93Urbano/WBC/SW/Wifi_web/Wifi_web.ino

/*
 WiFi Web Server LED Blink

 A simple web server that lets you blink an LED via the web.
 This sketch will print the IP address of your WiFi Shield (once connected)
 to the Serial monitor. From there, you can open that address in a web browser
 to turn on and off the LED on pin 5.

 If the IP address of your shield is yourAddress:
 http://yourAddress/H turns the LED on
 http://yourAddress/L turns it off

 This example is written for a network using WPA2 encryption. For insecure
 WEP or WPA, change the Wifi.begin() call and use Wifi.setMinSecurity() accordingly.

 Circuit:
 * WiFi shield attached
 * LED attached to pin 5

 created for arduino 25 Nov 2012
 by Tom Igoe

ported for sparkfun esp32 
31.01.2017 by Jan Hendrik Berlin
 
 */

#include <WiFi.h>

//concatenacion de cadenas
#include <iostream>
#include <cstdio>  

const char* ssid     = "Galaxy S20+b24a";
const char* password = "davidjimenez";

WiFiServer server(80);

// Variable to store the HTTP request
String header;

// Auxiliar variables to store the current output state
String output26State = "off";
String output27State = "off";

// Assign output variables to GPIO pins
const int output26 = 0;
const int output27 = 1;

void setup()
{
    Serial.begin(115200);

    delay(10);

    // We start by connecting to a WiFi network

    Serial.println();
    Serial.println();
    Serial.print("Connecting to ");
    Serial.println(ssid);

    WiFi.begin(ssid, password);

    while (WiFi.status() != WL_CONNECTED) {
        delay(500);
        Serial.print(".");
    }

    // Initialize the output variables as outputs
    pinMode(output26, OUTPUT);
    pinMode(output27, OUTPUT);
    // Set outputs to LOW
    digitalWrite(output26, LOW);
    digitalWrite(output27, LOW);

    Serial.println("");
    Serial.println("WiFi connected.");
    Serial.println("IP address: ");
    Serial.println(WiFi.localIP());
    
    server.begin();

}

void loop(){
 WiFiClient client = server.available();   // listen for incoming clients

  if (client) {                             // if you get a client,
    Serial.println("New Client.");           // print a message out the serial port
    String currentLine = "";                // make a String to hold incoming data from the client
    while (client.connected()) {            // loop while the client's connected
      if (client.available()) {             // if there's bytes to read from the client,
        char c = client.read();             // read a byte, then
        Serial.write(c);                    // print it out the serial monitor
        if (c == '\n') {                    // if the byte is a newline character

          // if the current line is blank, you got two newline characters in a row.
          // that's the end of the client HTTP request, so send a response:
          if (currentLine.length() == 0) {
            // HTTP headers always start with a response code (e.g. HTTP/1.1 200 OK)
            // and a content-type so the client knows what's coming, then a blank line:
            client.println("HTTP/1.1 200 OK");
            client.println("Content-type:text/html");
            client.println();

            // the content of the HTTP response follows the header:
            client.print("Click <a href=\"/H\">here</a> to turn the LED on pin 5 on.<br>");
            client.print("Click <a href=\"/L\">here</a> to turn the LED on pin 5 off.<br>");

            // turns the GPIOs on and off
            if (header.indexOf("GET /26/on") >= 0) {
              printf("GPIO 26 on");
              output26State = "on";
              digitalWrite(0, HIGH); 
            } else if (header.indexOf("GET /26/off") >= 0) {
              Serial.println("GPIO 26 off");
              output26State = "off";
              digitalWrite(0, LOW); 
            } else if (header.indexOf("GET /27/on") >= 0) {
              Serial.println("GPIO 27 on");
              output27State = "on";
              digitalWrite(0, HIGH); 
            } else if (header.indexOf("GET /27/off") >= 0) {
              Serial.println("GPIO 27 off");
              output27State = "off";
              digitalWrite(0, LOW); 
            }
            
           // Display the HTML web page
          client.println("<!DOCTYPE html><html>");
          client.println("<head><meta name=\"viewport\" content=\"width=device-width, initial-scale=1\">");
          client.println("<link rel=\"icon\" href=\"data:,\">");
          // CSS to style the on/off buttons and terminal
          client.println("<style>html { font-family: Helvetica; display: inline-block; margin: 0px auto; text-align: center;}");
          client.println(".button { background-color: #4CAF50; border: none; color: white; padding: 16px 40px;");
          client.println("text-decoration: none; font-size: 30px; margin: 2px; cursor: pointer;}");
          client.println(".button2 {background-color: #555555;}");
          client.println(".terminal { width: 80%; height: 300px; overflow: scroll; border: 1px solid #ccc; padding: 10px; margin: 10px auto;}");
          client.println("</style></head>");

          // Web Page Heading
          client.println("<body><h1>ESP32 Web Server</h1>");

          // Terminal Section
          client.println("<div class=\"terminal\" id=\"terminal\">Welcome to the ESP32 Terminal</div>");

          // Dropdown (select) for options
          client.println("<select id=\"dropdown\">");
          client.println("<option value=\"option1\">Option 1</option>");
          client.println("<option value=\"option2\">Option 2</option>");
          client.println("<option value=\"option3\">Option 3</option>");
          client.println("</select>");

          // Button to send a command
          client.println("<button class=\"button\" onclick=\"sendCommand()\">Send Command</button>");

          // JavaScript for handling command submission
          client.println("<script>");
          client.println("function sendCommand() {");
          client.println("  var dropdown = document.getElementById('dropdown');");
          client.println("  var selectedOption = dropdown.options[dropdown.selectedIndex].value;");
          client.println("  var terminal = document.getElementById('terminal');");
          client.println("  terminal.innerHTML += '<p>Sent command: ' + selectedOption + '</p>';");
          client.println("}");
          client.println("</script>");

          client.println("</body></html>");

            
            // Display current state, and ON/OFF buttons for GPIO 26  
            client.println("<p>GPIO 26 - State " + output26State + "</p>");
            // If the output26State is off, it displays the ON button       
            if (output26State=="off") {
              client.println("<p><a href=\"/26/on\"><button class=\"button\">ON</button></a></p>");
            } else {
              client.println("<p><a href=\"/26/off\"><button class=\"button button2\">OFF</button></a></p>");
            } 
               
            // Display current state, and ON/OFF buttons for GPIO 27  
            client.println("<p>GPIO 27 - State " + output27State + "</p>");
            // If the output27State is off, it displays the ON button       
            if (output27State=="off") {
              client.println("<p><a href=\"/27/on\"><button class=\"button\">ON</button></a></p>");
            } else {
              client.println("<p><a href=\"/27/off\"><button class=\"button button2\">OFF</button></a></p>");
            }
            client.println("</body></html>");

            // The HTTP response ends with another blank line:
            client.println();
            // break out of the while loop:
            break;
          } else {    // if you got a newline, then clear currentLine:
            currentLine = "";
          }
        } else if (c != '\r') {  // if you got anything else but a carriage return character,
          currentLine += c;      // add it to the end of the currentLine
        }

        // Check to see if the client request was "GET /H" or "GET /L":
        if (currentLine.endsWith("GET /H")) {
          digitalWrite(0, HIGH);               // GET /H turns the LED on
        }
        if (currentLine.endsWith("GET /L")) {
          digitalWrite(0, LOW);                // GET /L turns the LED off
        }
      }
    }
    // close the connection:
    // Clear the header variable
    header = "";
    client.stop();
    Serial.println("Client Disconnected.");
  }
}
