93Urbano/WBC/SW/mainstandby/CAN.hpp

//************************************//
//              CAN.hpp               //
//************************************//

#include "driver/gpio.h"
#include "driver/twai.h"

#define CANTX GPIO_NUM_46
#define CANRX GPIO_NUM_3
